jpskenn/SandyLP/assets/Readme/DSC_8155.jpeg

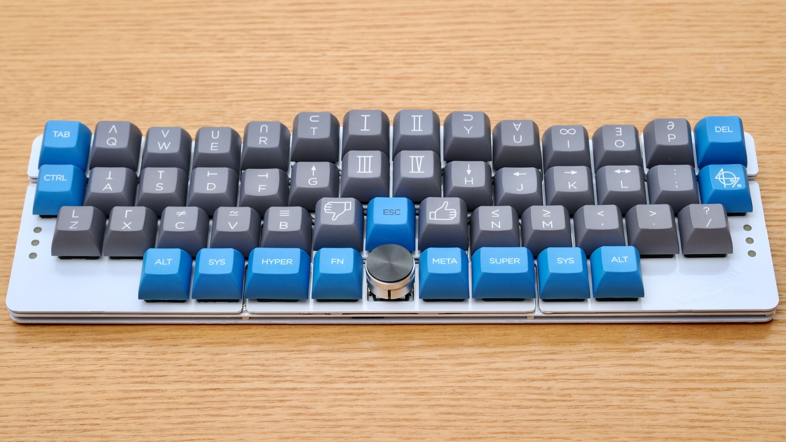
assets/Readme/DSC_8155.jpeg
