jpskenn/SandyLP/assets/Readme/DSC_8162.jpeg

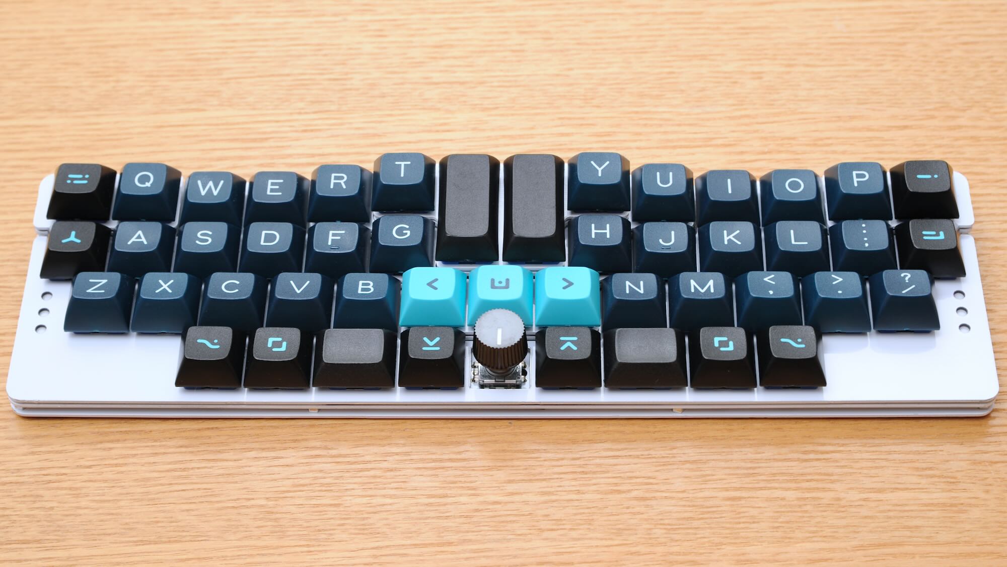
assets/Readme/DSC_8162.jpeg
