jpskenn/SandyLP/assets/BuildGuide_DN0010/pcb_top_front.png

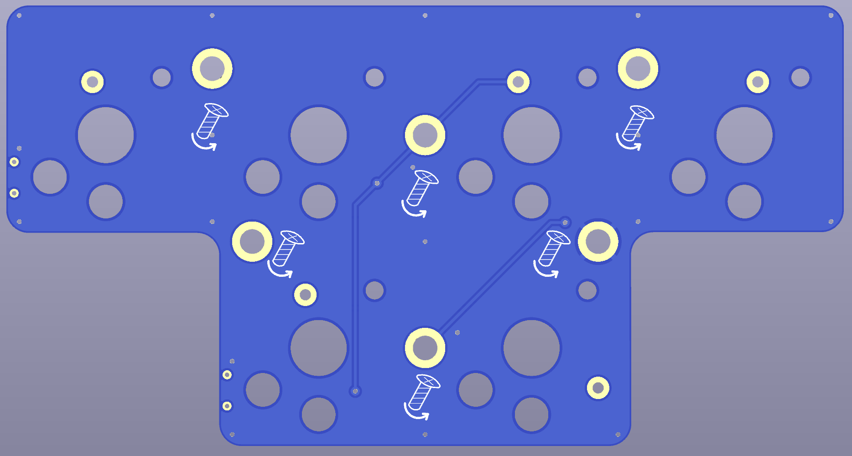
assets/BuildGuide_DN0010/pcb_top_front.png
